lingex/TimerV2.0/Doc/000.jpg

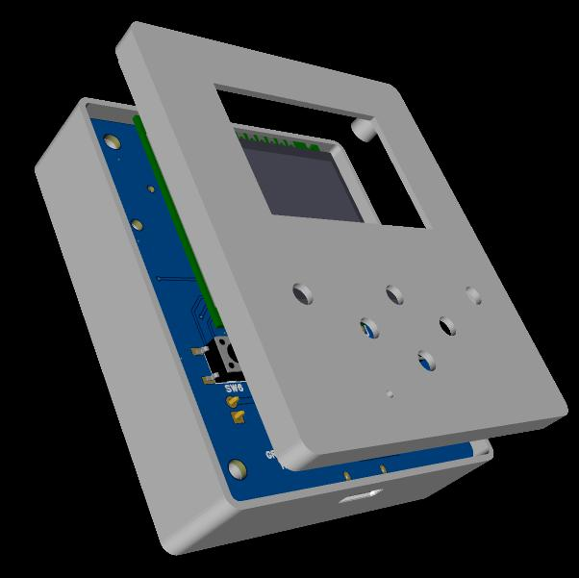
Doc/000.jpg
