lingex/TimerV2.0/Doc/001.jpg

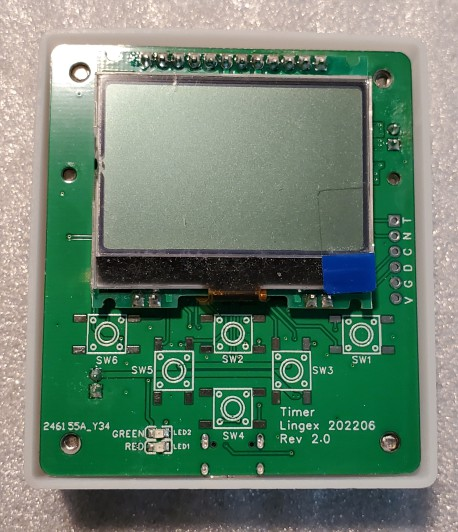
Doc/001.jpg
