lingex/TimerV2.0/Doc/002.jpg

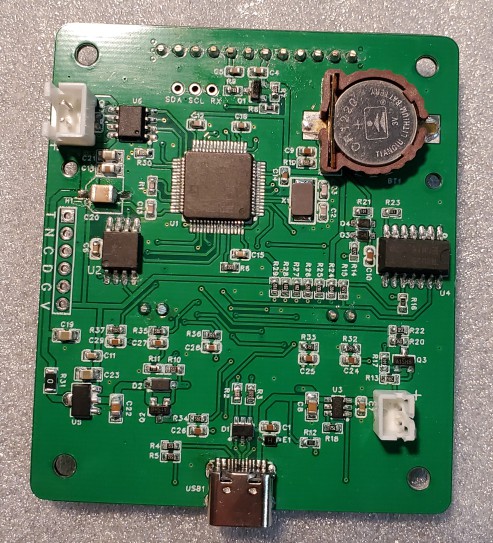
Doc/002.jpg
