lingex/TimerV2.0/Doc/003.jpg

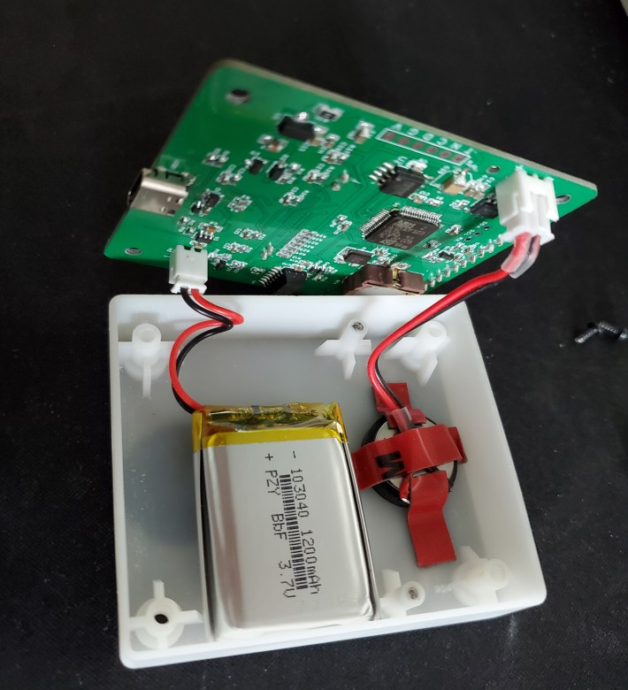
Doc/003.jpg
