lingex/TimerV2.0/Doc/005.jpg

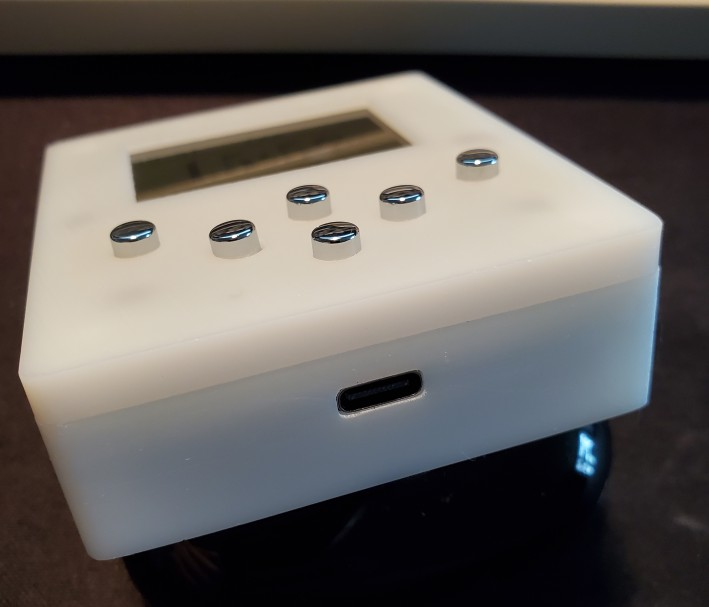
Doc/005.jpg
