lingex/TimerV2.0/Doc/006.jpg

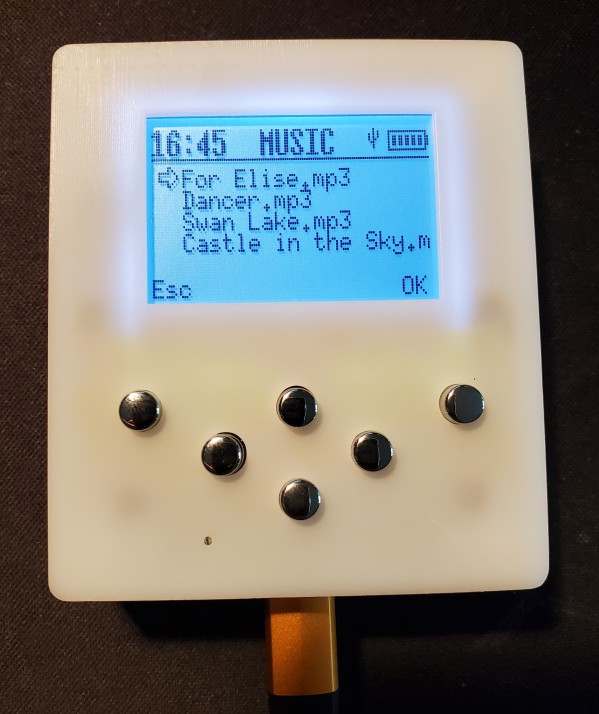
Doc/006.jpg
