lingex/TimerV2.0/TimerApp/Core/Src/spi_flash.c

/*******************************************************************************
* Module Name      : spi_flash.c
* Create Date      : 2016-08-02
* Author           : huanglong
* Copyright        :
* Description      : 外部 SPI FLASH
* Revision History :
* Date          Author        Version        Notes
  2016-08-02    huanglong     V1.0           创建
*******************************************************************************/

/* 包含头文件 ----------------------------------------------------------------*/
#include "spi_flash.h"

extern SPI_HandleTypeDef hspi3;

uint8_t W25QXX_BUFFER[SPI_FLASH_WRITE_BUFFER_LEN];
uint16_t W25QXX_TYPE = W25Q16;             // 默认是W25Q16

volatile int g_WrOver = 0;
volatile int g_RdOver = 0;

uint8_t powerState = 1;

uint8_t SPI_ReadWriteByte(uint8_t TxData)
{
  uint8_t Rxdata;
  HAL_SPI_TransmitReceive(&hspi3, &TxData, &Rxdata, 1, 100);
   return Rxdata;                          // 返回收到的数据
}

// 4Kbytes为一个Sector
// 16个扇区为1个Block
// W25Q256 容量为32M字节,共有512个Block,8192个Sector
// 初始化SPI FLASH的IO口
void W25QXX_Init(void)
{
  uint8_t temp;
  W25QXX_TYPE = W25QXX_ReadID();           // 读取FLASH ID.
  if(W25QXX_TYPE == W25Q256)               // SPI FLASH为W25Q256
  {
    temp = W25QXX_ReadSR(3);               // 读取状态寄存器3，判断地址模式
    if((temp & 0X01) == 0)                 // 如果不是4字节地址模式,则进入4字节地址模式
    {
      SF_CS_L;                             // 选中
      SPI_ReadWriteByte(W25X_Enable4ByteAddr);  // 发送进入4字节地址模式指令
      SF_CS_H;                             // 取消片选
    }
  }
}

// 读取W25QXX的状态寄存器，W25QXX一共有3个状态寄存器
// 状态寄存器1：
// BIT7  6   5   4   3   2   1   0
// SPR   RV  TB BP2 BP1 BP0 WEL BUSY
// SPR:默认0,状态寄存器保护位,配合WP使用
// TB,BP2,BP1,BP0:FLASH区域写保护设置
// WEL:写使能锁定
// BUSY:忙标记位(1,忙;0,空闲)
// 默认:0x00
// 状态寄存器2：
// BIT7  6   5   4   3   2   1   0
// SUS   CMP LB3 LB2 LB1 (R) QE  SRP1
// 状态寄存器3：
// BIT7      6    5    4   3   2   1   0
// HOLD/RST  DRV1 DRV0 (R) (R) WPS ADP ADS
// regno:状态寄存器号，范:1~3
// 返回值:状态寄存器值
uint8_t W25QXX_ReadSR(uint8_t regno)
{
  uint8_t byte=0,command=0;
  switch(regno)
  {
  case 1:
    command=W25X_ReadStatusReg1;           // 读状态寄存器1指令
    break;
  case 2:
    command=W25X_ReadStatusReg2;           // 读状态寄存器2指令
    break;
  case 3:
    command=W25X_ReadStatusReg3;           // 读状态寄存器3指令
    break;
  default:
    command=W25X_ReadStatusReg1;
    break;
  }
  SF_CS_L;                                 // 使能器件
  SPI_ReadWriteByte(command);              // 发送读取状态寄存器命令
  byte = SPI_ReadWriteByte(0Xff);          // 读取一个字节
  SF_CS_H;                                 // 取消片选
  return byte;
}

// 写W25QXX状态寄存器
void W25QXX_Write_SR(uint8_t regno, uint8_t sr)
{
  uint8_t command=0;
  switch(regno)
  {
  case 1:
    command=W25X_WriteStatusReg1;          // 写状态寄存器1指令
    break;
  case 2:
    command=W25X_WriteStatusReg2;          // 写状态寄存器2指令
    break;
  case 3:
    command=W25X_WriteStatusReg3;          // 写状态寄存器3指令
    break;
  default:
    command=W25X_WriteStatusReg1;
    break;
  }
  SF_CS_L;                                 // 使能器件
  SPI_ReadWriteByte(command);              // 发送写取状态寄存器命令
  SPI_ReadWriteByte(sr);                   // 写入一个字节
  SF_CS_H;                                 // 取消片选
}

// W25QXX写使能
// 将WEL置位
void W25QXX_Write_Enable(void)
{
  SF_CS_L;                                 // 使能器件
  SPI_ReadWriteByte(W25X_WriteEnable);     // 发送写使能
  SF_CS_H;                                 // 取消片选
}

// W25QXX写禁止
// 将WEL清零
void W25QXX_Write_Disable(void)
{
  SF_CS_L;                                 // 使能器件
  SPI_ReadWriteByte(W25X_WriteDisable);    // 发送写禁止指令
  SF_CS_H;                                 // 取消片选
}

// 读取芯片ID
// 返回值如下:
// 0XEF13,表示芯片型号为W25Q80
// 0XEF14,表示芯片型号为W25Q16
// 0XEF15,表示芯片型号为W25Q32
// 0XEF16,表示芯片型号为W25Q64
// 0XEF17,表示芯片型号为W25Q128
// 0XEF18,表示芯片型号为W25Q256
uint16_t W25QXX_ReadID(void)
{
  uint16_t Temp = 0;
  SF_CS_L;
  SPI_ReadWriteByte(0x90);                 // 发送读取ID命令
  SPI_ReadWriteByte(0x00);
  SPI_ReadWriteByte(0x00);
  SPI_ReadWriteByte(0x00);
  Temp|=SPI_ReadWriteByte(0xFF)<<8;
  Temp|=SPI_ReadWriteByte(0xFF);
  SF_CS_H;
  return Temp;
}

// 读取SPI FLASH
// 在指定地址开始读取指定长度的数据
// pBuffer:数据存储区
// ReadAddr:开始读取的地址(24bit)
// NumByteToRead:要读取的字节数(最大65535)
void W25QXX_Read(uint8_t* pBuffer, uint32_t ReadAddr, uint16_t NumByteToRead)
{
  // uint16_t i;
  SF_CS_L;                                        // 使能器件
  SPI_ReadWriteByte(W25X_ReadData);               // 发送读取命令
  if(W25QXX_TYPE == W25Q256)                      // 如果是W25Q256的话地址为4字节的，要发送最高8位
  {
      SPI_ReadWriteByte((uint8_t)((ReadAddr)>>24));
  }
  SPI_ReadWriteByte((uint8_t)((ReadAddr)>>16));   // 发送24bit地址
  SPI_ReadWriteByte((uint8_t)((ReadAddr)>>8));
  SPI_ReadWriteByte((uint8_t)ReadAddr);

  // for(i=0;i<NumByteToRead;i++)
  // {
    // pBuffer[i]=SPI_ReadWriteByte(0XFF);           // 循环读数
  // }

#if SPI_FLASH_DMA_ENABLE
  g_RdOver = 0;
  HAL_SPI_Receive_DMA(&hspi3, pBuffer, NumByteToRead);
  //HAL_SPI_Receive_IT(&hspi3, pBuffer, NumByteToRead);

  uint32_t tick = HAL_GetTick();
  uint32_t timeout = tick + NumByteToRead * 10;
  while (g_RdOver == 0 && HAL_GetTick() < timeout);
#else
  if (HAL_SPI_Receive(&hspi3, pBuffer, NumByteToRead, NumByteToRead * 10) != HAL_OK)
  {
	Error_Handler();
  }
#endif

  SF_CS_H;
}

// SPI在一页(0~65535)内写入少于256个字节的数据
// 在指定地址开始写入最大256字节的数据
// pBuffer:数据存储区
// WriteAddr:开始写入的地址(24bit)
// NumByteToWrite:要写入的字节数(最大256),该数不应该超过该页的剩余字节数!!!
void W25QXX_Write_Page(uint8_t* pBuffer,uint32_t WriteAddr,uint16_t NumByteToWrite)
{
  // uint16_t i;
  W25QXX_Write_Enable();                          // SET WEL
  SF_CS_L;                                        // 使能器件
  SPI_ReadWriteByte(W25X_PageProgram);            // 发送写页命令
  if (W25QXX_TYPE == W25Q256)                     // 如果是W25Q256的话地址为4字节的，要发送最高8位
  {
    SPI_ReadWriteByte((uint8_t)((WriteAddr)>>24));
  }
  SPI_ReadWriteByte((uint8_t)((WriteAddr)>>16));  // 发送24bit地址
  SPI_ReadWriteByte((uint8_t)((WriteAddr)>>8));
  SPI_ReadWriteByte((uint8_t)WriteAddr);

  // for(i=0; i<NumByteToWrite; i++) SPI_ReadWriteByte(pBuffer[i]);  // 循环写数

#if SPI_FLASH_DMA_ENABLE
  g_WrOver = 0;
  HAL_SPI_Transmit_DMA(&hspi3, pBuffer, NumByteToWrite);

  uint32_t tick = HAL_GetTick();
  uint32_t timeout = tick + NumByteToWrite * 20;
  while (g_WrOver == 0 && HAL_GetTick() < timeout);
#else 
	HAL_SPI_Transmit(&hspi3, pBuffer, NumByteToWrite, NumByteToWrite * 5);
#endif

  SF_CS_H;                                                        // 取消片选
  W25QXX_Wait_Busy();                                             // 等待写入结束
}

void HAL_SPI_RxCpltCallback(SPI_HandleTypeDef *hspi)
{
  g_RdOver = 1;
}
void HAL_SPI_TxCpltCallback(SPI_HandleTypeDef *hspi)
{
  g_WrOver = 1;
}

// 无检验写SPI FLASH
// 必须确保所写的地址范围内的数据全部为0XFF,否则在非0XFF处写入的数据将失败!
// 具有自动换页功能
// 在指定地址开始写入指定长度的数据,但是要确保地址不越界!
// pBuffer:数据存储区
// WriteAddr:开始写入的地址(24bit)
// NumByteToWrite:要写入的字节数(最大65535)
// CHECK OK
void W25QXX_Write_NoCheck(uint8_t* pBuffer,uint32_t WriteAddr,uint16_t NumByteToWrite)
{
  uint16_t pageremain;
  pageremain = 256-WriteAddr%256;                           // 单页剩余的字节数
  if(NumByteToWrite<=pageremain)pageremain=NumByteToWrite;  // 不大于256个字节
  while(1)
  {
    W25QXX_Write_Page(pBuffer,WriteAddr,pageremain);
    if (NumByteToWrite == pageremain) break;                // 写入结束了
    else                                                    // NumByteToWrite>pageremain
    {
      pBuffer+=pageremain;
      WriteAddr+=pageremain;

      NumByteToWrite-=pageremain;                           // 减去已经写入了的字节数
      if(NumByteToWrite>256) pageremain = 256;              // 一次可以写入256个字节
      else pageremain=NumByteToWrite;                       // 不够256个字节了
    }
  }
}

// 写SPI FLASH
// 在指定地址开始写入指定长度的数据
// 该函数带擦除操作!
// pBuffer:数据存储区
// WriteAddr:开始写入的地址(24bit)
// NumByteToWrite:要写入的字节数(最大65535)
void W25QXX_Write(uint8_t* pBuffer, uint32_t WriteAddr, uint16_t NumByteToWrite)
{
  uint32_t secpos;
  uint16_t secoff;
  uint16_t secremain;
  uint16_t i;
  uint8_t *pBuff = W25QXX_BUFFER;

  secpos=WriteAddr/4096;//扇区地址
  secoff=WriteAddr%4096;//在扇区内的偏移
  secremain=4096-secoff;//扇区剩余空间大小
  //printf("ad:%X,nb:%X\r\n",WriteAddr,NumByteToWrite);//测试用
  if(NumByteToWrite<=secremain)secremain=NumByteToWrite;//不大于4096个字节
  while(1)
  {
    W25QXX_Read(pBuff,secpos*4096,4096);//读出整个扇区的内容
    for(i=0;i<secremain;i++)//校验数据
    {
        if(pBuff[secoff+i]!=0XFF)break;//需要擦除
    }
    if(i<secremain)//需要擦除
    {
      W25QXX_Erase_Sector(secpos);//擦除这个扇区
      for(i=0;i<secremain;i++)       //复制
      {
          pBuff[i+secoff]=pBuffer[i];
      }
      W25QXX_Write_NoCheck(pBuff,secpos*4096,4096);//写入整个扇区
    }
	else
	{
		W25QXX_Write_NoCheck(pBuffer,WriteAddr,secremain);//写已经擦除了的,直接写入扇区剩余区间.
	}
    if(NumByteToWrite==secremain)
	{
		break;//写入结束了
	}
    else//写入未结束
    {
      secpos++;//扇区地址增1
      secoff=0;//偏移位置为0

      pBuffer+=secremain;  //指针偏移
      WriteAddr+=secremain;//写地址偏移
      NumByteToWrite-=secremain;                //字节数递减
      if(NumByteToWrite>4096)
	  {
		  secremain=4096;    //下一个扇区还是写不完
	  }
      else
	  {
		  secremain=NumByteToWrite;            //下一个扇区可以写完了
	  }
    }
  };
}

// 擦除整个芯片
// 等待时间超长
void W25QXX_Erase_Chip(void)
{
  W25QXX_Write_Enable();                  // SET WEL
  W25QXX_Wait_Busy();
  SF_CS_L;                                // 使能器件
  SPI_ReadWriteByte(W25X_ChipErase);      // 发送片擦除命令
  SF_CS_H;                                // 取消片选
  W25QXX_Wait_Busy();                     // 等待芯片擦除结束
}

// 擦除一个扇区
// Dst_Addr:扇区地址 根据实际容量设置
// 擦除一个扇区的最少时间:150ms
void W25QXX_Erase_Sector(uint32_t Dst_Addr)
{
  // 监视falsh擦除情况,测试用
  // printf("fe:%x\r\n",Dst_Addr);
  Dst_Addr*=4096;
  W25QXX_Write_Enable();                  // SET WEL
  W25QXX_Wait_Busy();
  SF_CS_L;                                // 使能器件
  SPI_ReadWriteByte(W25X_SectorErase);    // 发送扇区擦除指令
  if(W25QXX_TYPE==W25Q256)                // 如果是W25Q256的话地址为4字节的，要发送最高8位
  {
  SPI_ReadWriteByte((uint8_t)((Dst_Addr)>>24));
  }
  SPI_ReadWriteByte((uint8_t)((Dst_Addr)>>16));  // 发送24bit地址
  SPI_ReadWriteByte((uint8_t)((Dst_Addr)>>8));
  SPI_ReadWriteByte((uint8_t)Dst_Addr);
  SF_CS_H;                                // 取消片选
  W25QXX_Wait_Busy();                     // 等待擦除完成
}

// 等待空闲
void W25QXX_Wait_Busy(void)
{
  while((W25QXX_ReadSR(1)&0x01)==0x01);   // 等待BUSY位清空
}

// 进入掉电模式
void W25QXX_PowerDown(void)
{
  SF_CS_L;                              // 使能器件
  SPI_ReadWriteByte(W25X_PowerDown);    // 发送掉电命令
  SF_CS_H;                              // 取消片选
  //delay_us(3);                          // 等待TPD

  HAL_SPI_MspDeInit(&hspi3);
  powerState = 0;
}

// 唤醒
void W25QXX_WAKEUP(void)
{
	HAL_SPI_MspInit(&hspi3);

  SF_CS_L;                                   // 使能器件
  SPI_ReadWriteByte(W25X_ReleasePowerDown);  // send W25X_PowerDown command 0xAB
  SF_CS_H;                                   // 取消片选
  //delay_us(3);                               // 等待TRES1
  powerState = 1;
}

uint32_t W25QXX_GetSectorCount(void)
{
	uint32_t sectorCount = 1;
	switch (W25QXX_TYPE)
	{
	case W25Q256:
		sectorCount = 65536;
		break;
	case W25Q128:
		sectorCount = 32768;
		break;
	case W25Q64:
		sectorCount = 16384;
		break;
	case W25Q32:
		sectorCount = 8192;
		break;
	case W25Q16:
		sectorCount = 4096;
		break;
	case W25Q80:
		sectorCount = 2048;
		break;
	default:
		break;
	}
	return sectorCount;
}

uint8_t W25QXX_GetPowerState(void)
{
	return powerState;
}
