lingex/TimerV2.0/TimerApp/Core/Inc/lcd.h

#ifndef __LCD_H__
#define __LCD_H__

#ifdef __cplusplus
extern "C" {
#endif

#include "main.h"
#include "u8g2.h"
#include "u8x8.h"

// LCD_CS
#define LCD_CS_SET HAL_GPIO_WritePin(LCD_CS_GPIO_Port, LCD_CS_Pin, GPIO_PIN_SET)
#define LCD_CS_RESET HAL_GPIO_WritePin(LCD_CS_GPIO_Port, LCD_CS_Pin, GPIO_PIN_RESET)

// LCD_RST
#define LCD_RST_SET HAL_GPIO_WritePin(LCD_RST_GPIO_Port, LCD_RST_Pin, GPIO_PIN_SET)
#define LCD_RST_RESET HAL_GPIO_WritePin(LCD_RST_GPIO_Port, LCD_RST_Pin, GPIO_PIN_RESET)

// LCD_DC
#define LCD_DC_SET HAL_GPIO_WritePin(LCD_DC_GPIO_Port, LCD_DC_Pin, GPIO_PIN_SET)
#define LCD_DC_RESET HAL_GPIO_WritePin(LCD_DC_GPIO_Port, LCD_DC_Pin, GPIO_PIN_RESET)

uint8_t u8x8_byte_hw_spi(u8x8_t *u8x8, uint8_t msg, uint8_t arg_int, void *arg_ptr);
uint8_t u8x8_gpio_and_delay(u8x8_t *u8x8, uint8_t msg, uint8_t arg_int, void *arg_ptr);
void u8g2Init(u8g2_t *u8g2, SPI_HandleTypeDef* hspi);

#ifdef __cplusplus
}
#endif

#endif
